FeruzTopalov/eleph/Supplementary/Pictures/UserManual/AnotherDevice.png

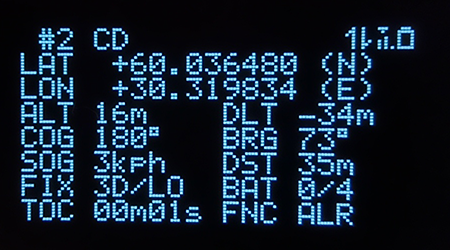
Supplementary/Pictures/UserManual/AnotherDevice.png
