FeruzTopalov/eleph/Supplementary/Pictures/UserManual/DeleteDevice.png

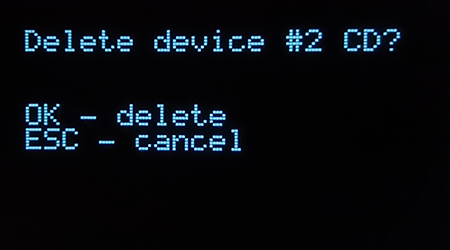
Supplementary/Pictures/UserManual/DeleteDevice.png
