FeruzTopalov/eleph/Supplementary/Pictures/UserManual/Devices.png

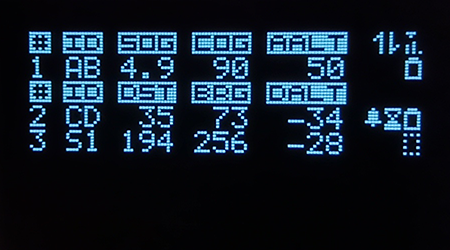
Supplementary/Pictures/UserManual/Devices.png
