FeruzTopalov/eleph/Supplementary/Pictures/UserManual/Main.png

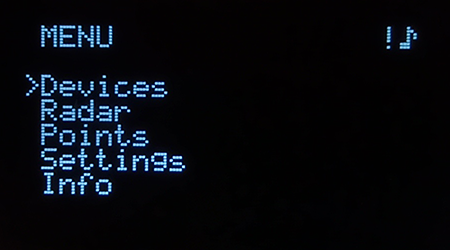
Supplementary/Pictures/UserManual/Main.png
