FeruzTopalov/eleph/Supplementary/Pictures/UserManual/MemoryPoint.png

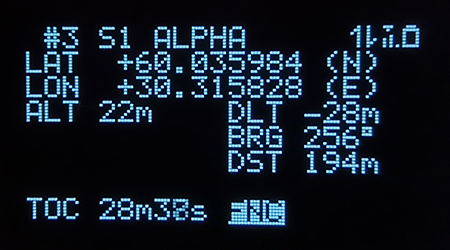
Supplementary/Pictures/UserManual/MemoryPoint.png
