FeruzTopalov/eleph/Supplementary/Pictures/UserManual/PointLoad.png

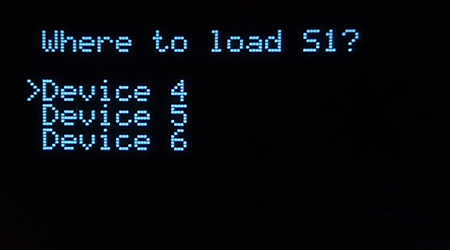
Supplementary/Pictures/UserManual/PointLoad.png
