FeruzTopalov/eleph/Supplementary/Pictures/UserManual/Points.png

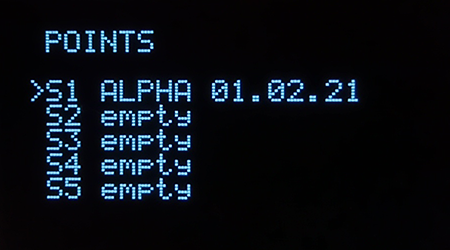
Supplementary/Pictures/UserManual/Points.png
