FeruzTopalov/eleph/Supplementary/Pictures/UserManual/Radar.png

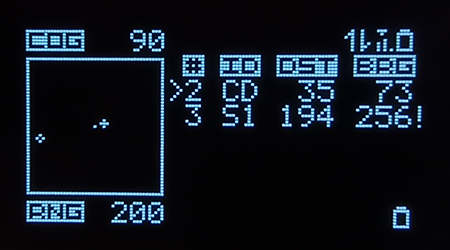
Supplementary/Pictures/UserManual/Radar.png
