FeruzTopalov/eleph/Supplementary/Pictures/UserManual/RadarHide1.png

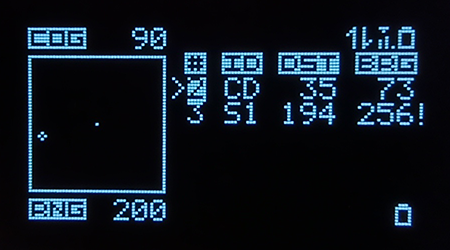
Supplementary/Pictures/UserManual/RadarHide1.png
