FeruzTopalov/eleph/Supplementary/Pictures/UserManual/RadarMemoryPoint.png

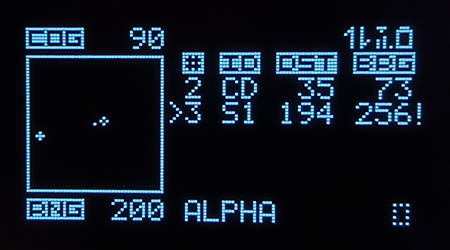
Supplementary/Pictures/UserManual/RadarMemoryPoint.png
