FeruzTopalov/eleph/Supplementary/Pictures/UserManual/SaveDevice.png

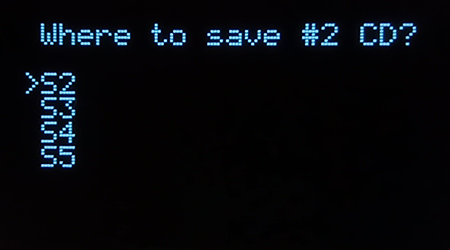
Supplementary/Pictures/UserManual/SaveDevice.png
