FeruzTopalov/eleph/Supplementary/Pictures/UserManual/ThisDevice.png

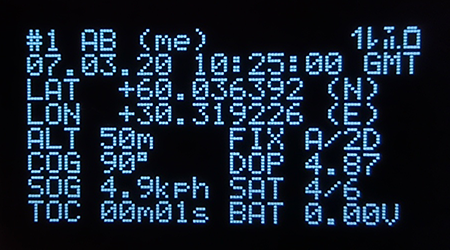
Supplementary/Pictures/UserManual/ThisDevice.png
